Hanz-Tech/vltone-midi-clock-mod/pics/IMG_8899.jpg

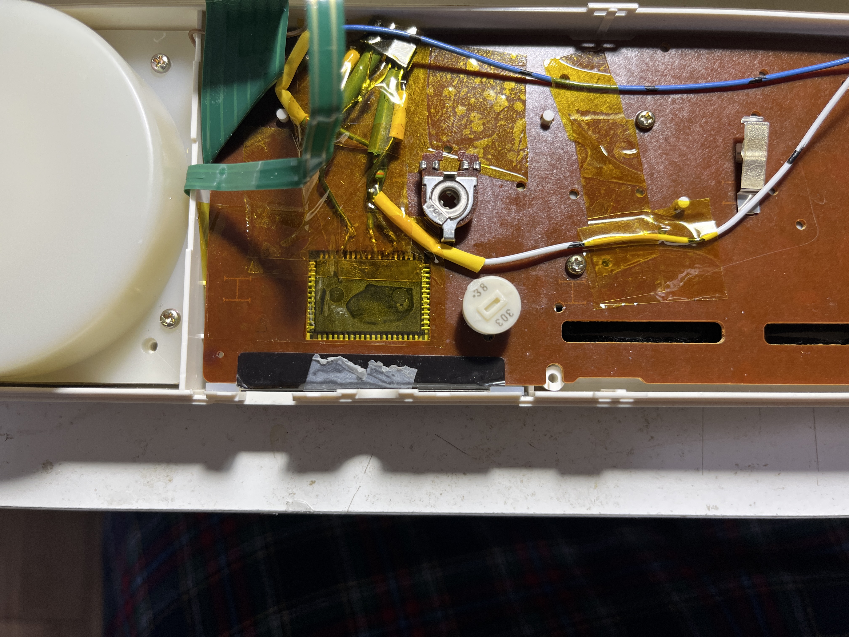
pics/IMG_8899.jpg
